RepRapLtd/MasterSpool/STLs/b-mid-l-3off.stl

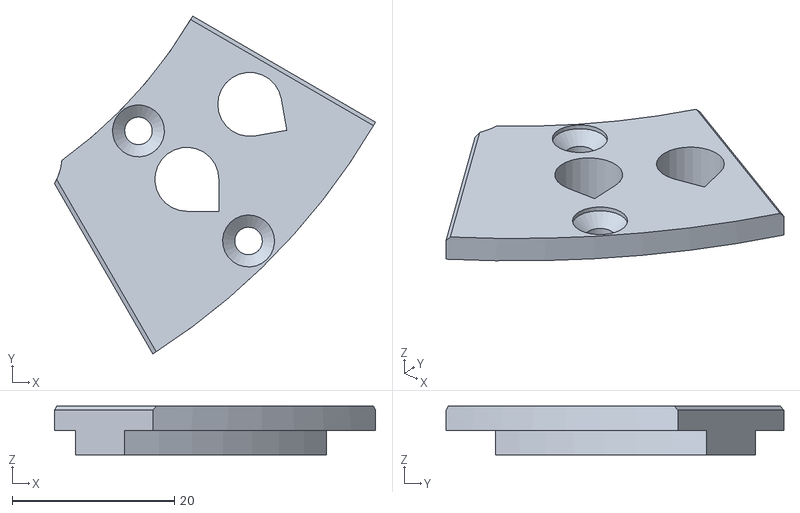
[picture p18: CAD file, 2019-04-03]
STLs/b-mid-l-3off.stl
39.5 x 41.6 x 6.00
