RepRapLtd/MasterSpool/STLs/b-outer-slot-3off.stl

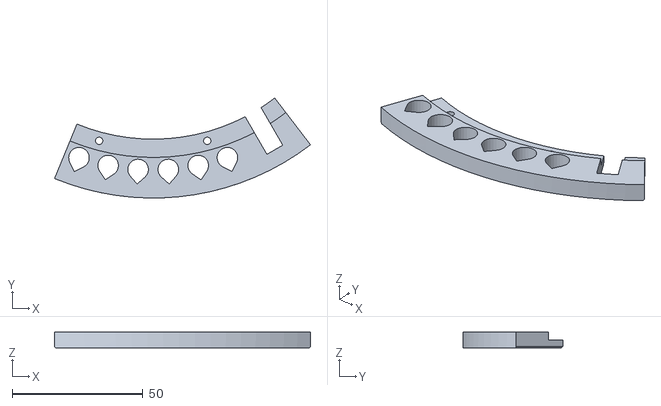
[picture p19: CAD file, 2019-04-03]
STLs/b-outer-slot-3off.stl
97.9 x 38.2 x 6.00
