RepRapLtd/MasterSpool/STLs/b-mid-r-3off.stl

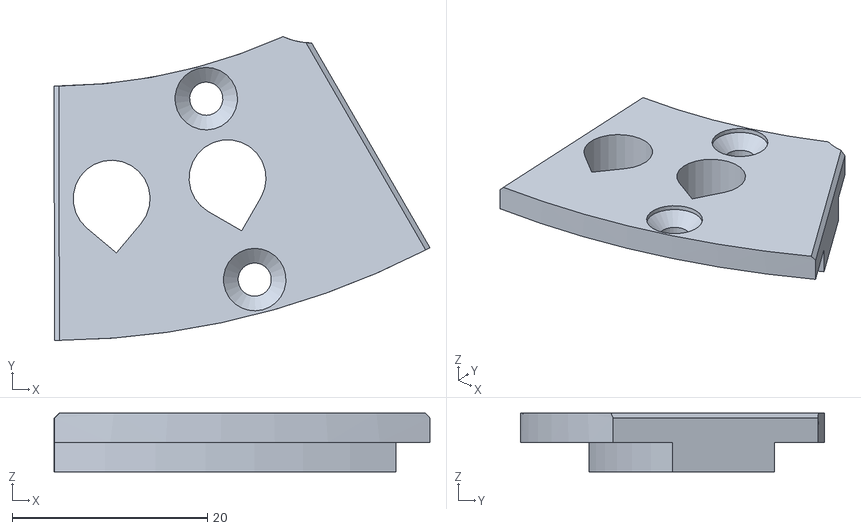
[picture p20: CAD file, 2019-04-03]
STLs/b-mid-r-3off.stl
38.5 x 31.1 x 6.00
