RepRapLtd/MasterSpool/STLs/b-inner-r-3off.stl

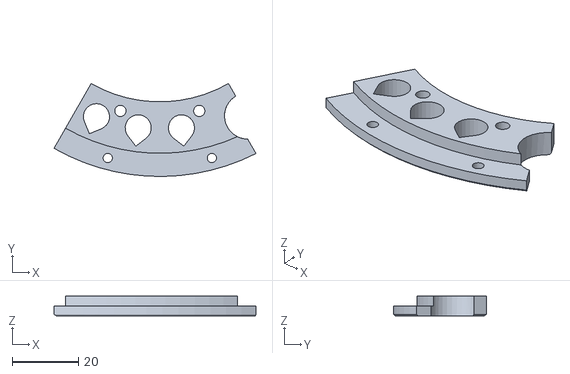
[picture p21: CAD file, 2019-04-03]
STLs/b-inner-r-3off.stl
60.9 x 28.0 x 6.00
