RepRapLtd/MasterSpool/STLs/b-outer-master-1off.stl

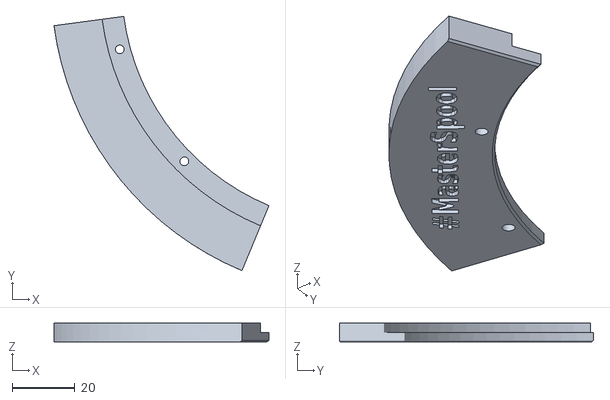
[picture p22: CAD file, 2019-04-03]
STLs/b-outer-master-1off.stl
68.7 x 81.3 x 6.00
