RepRapLtd/MasterSpool/STLs/t-outer-slot-3off.stl

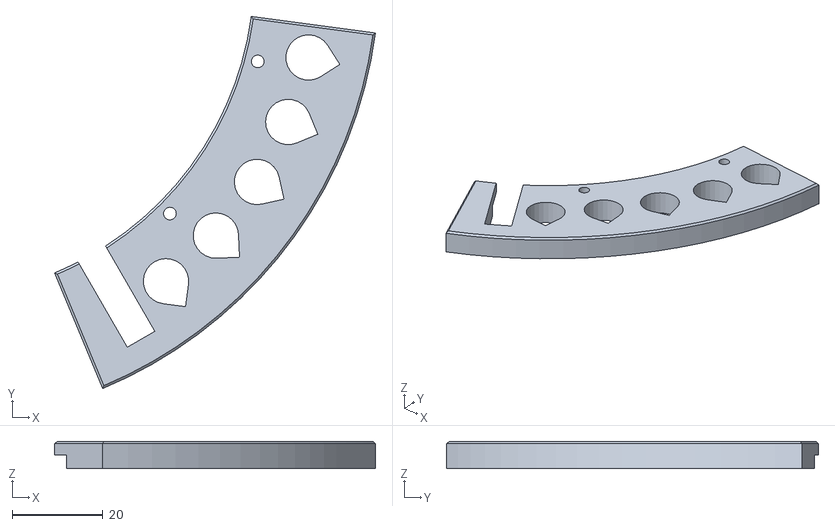
[picture p23: CAD file, 2019-04-03]
STLs/t-outer-slot-3off.stl
70.7 x 82.0 x 6.00
