RepRapLtd/MasterSpool/STLs/t-mid-slot-l-3off.stl

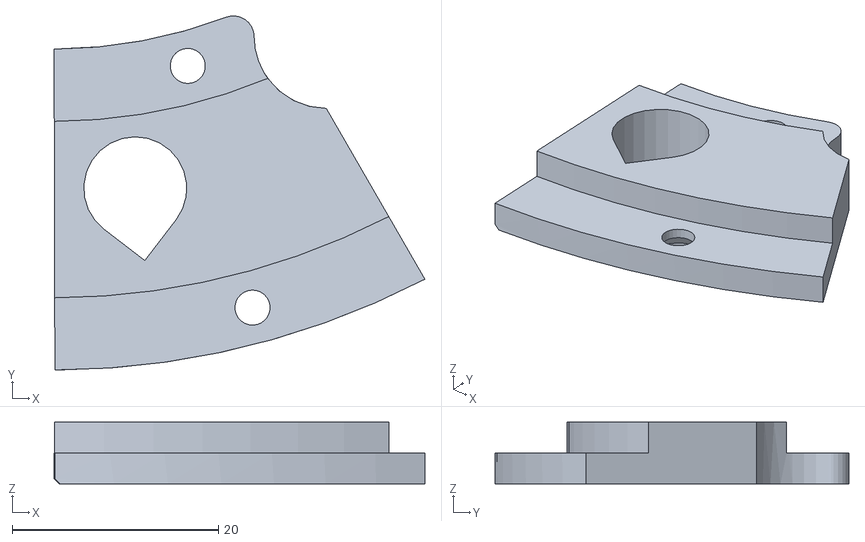
[picture p24: CAD file, 2019-04-03]
STLs/t-mid-slot-l-3off.stl
35.9 x 34.3 x 6.00
