RepRapLtd/MasterSpool/STLs/t-outer-tube-2off.stl

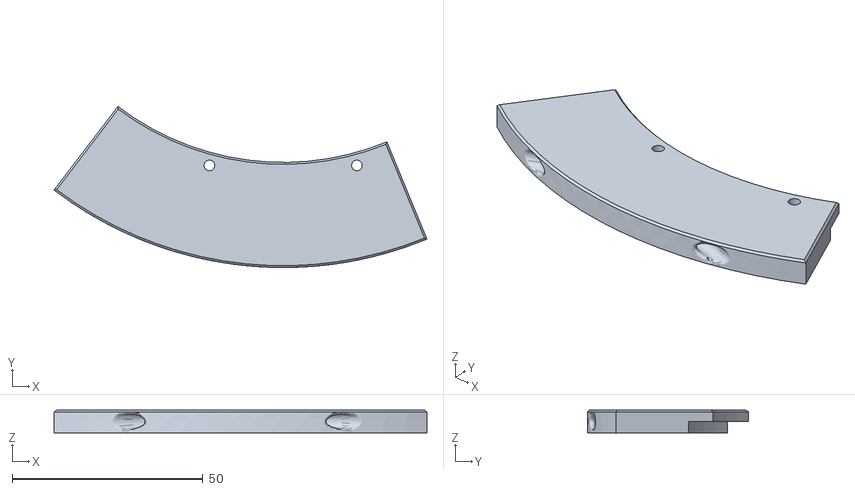
[picture p25: CAD file, 2019-04-03]
STLs/t-outer-tube-2off.stl
97.9 x 42.3 x 6.00
